elinucknack/door-sensor/door-sensor-pcb.kicad_sch

## KiCad design door-sensor-pcb.kicad_sch (2025-08-03)

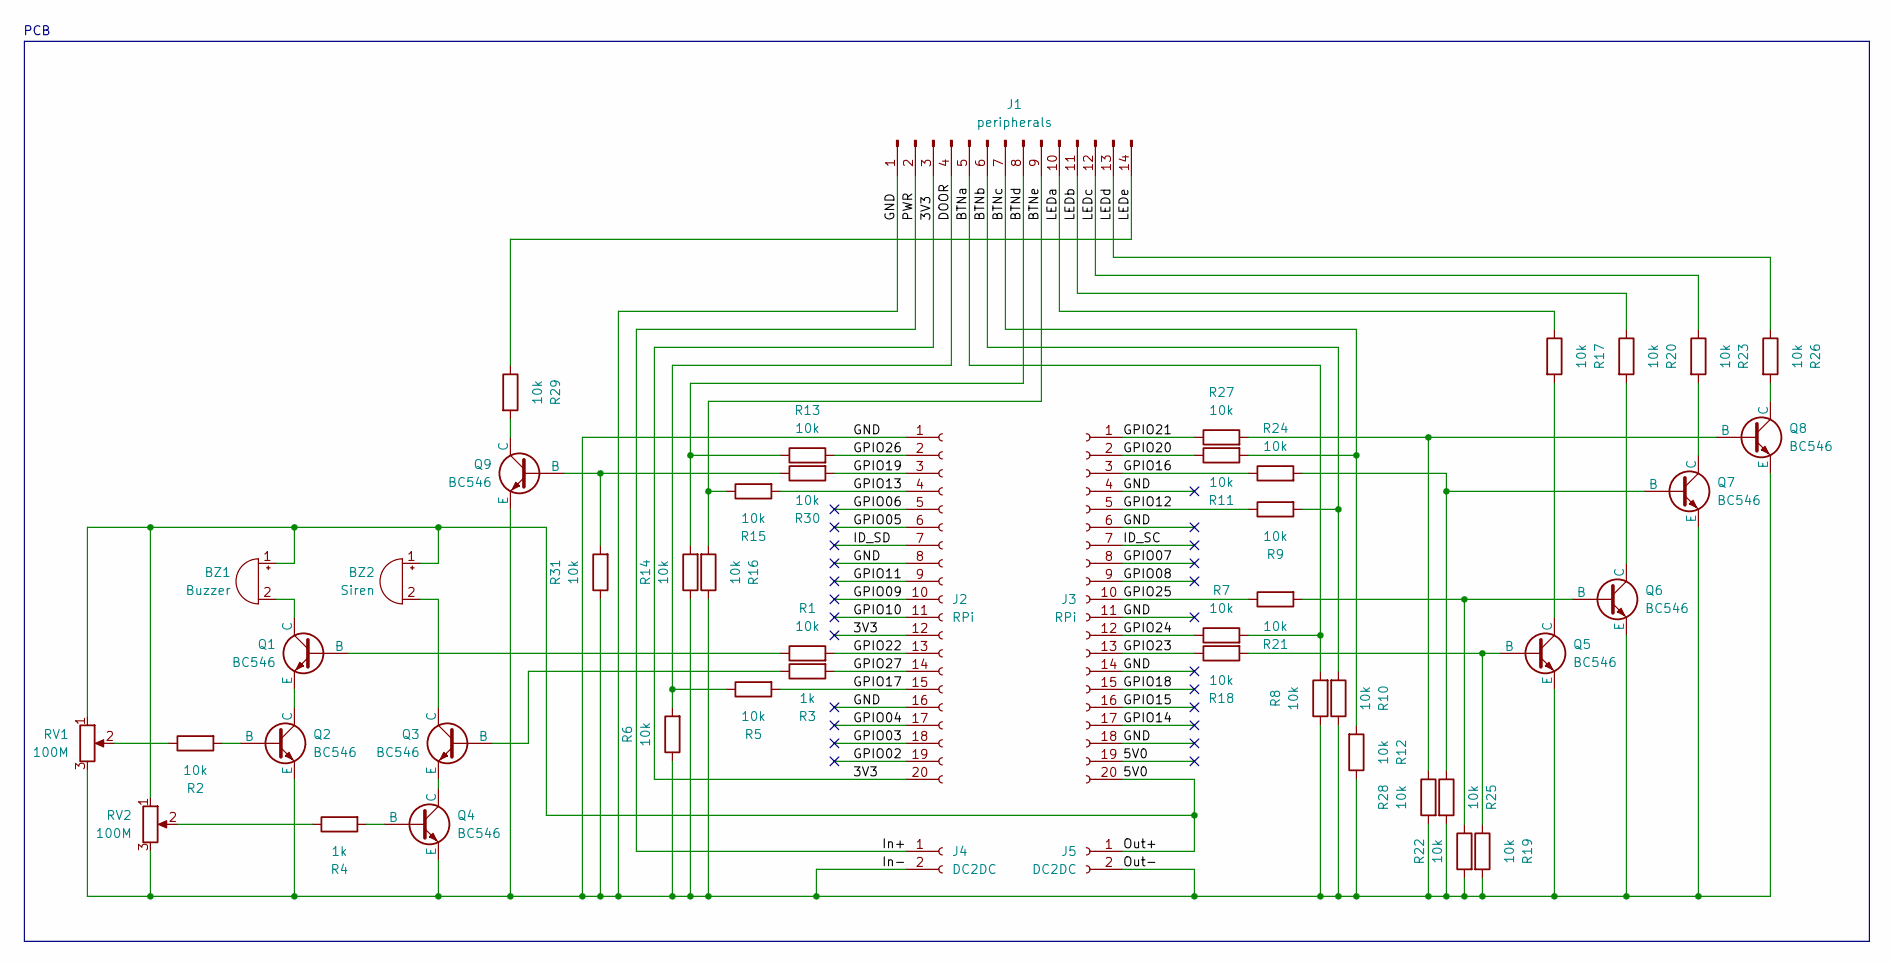
[picture p12: schematic door-sensor-pcb.kicad_sch]

Parts:
BZ1: Buzzer
BZ2: Siren
J1: peripherals
J2, J3: RPi
J4, J5: DC2DC
Q1, Q2, Q3, Q4, Q5, Q6, Q7, Q8, Q9: BC546
R1, R2, R5, R6, R7, R8, R9, R10, R11, R12, R13, R14, R15, R16, R17, R18, R19, R20, R21, R22, R23, R24, R25, R26, R27, R28, R29, R30, R31: 10k
R3, R4: 1k
RV1, RV2: 100M

Connections:
3V3: J1.3, J2.12, J2.20
5V0: BZ1.1 (+), BZ2.1 (+), J3.19, J3.20, J5.1, RV1.1, RV2.1
BTNa: J1.5, R7.2, R8.2
BTNb: J1.6, R9.2, R10.2
BTNc: J1.7, R11.2, R12.2
BTNd: J1.8, R13.1, R14.2
BTNe: J1.9, R15.1, R16.2
DOOR: J1.4, R5.1, R6.2
GND: J1.1, J2.1, J2.8, J2.16, J3.4, J3.6, J3.11, J3.14, J3.18, J4.2, J5.2, Q2.3 (E), Q4.3 (E), Q5.3 (E), Q6.3 (E), Q7.3 (E), Q8.3 (E), Q9.3 (E), R6.1, R8.1, R10.1, R12.1, R14.1, R16.1, R19.2, R22.2, R25.2, R28.2, R31.1, RV1.3, RV2.3
GPIO02: J2.19
GPIO03: J2.18
GPIO04: J2.17
GPIO05: J2.6
GPIO06: J2.5
GPIO07: J3.8
GPIO08: J3.9
GPIO09: J2.10
GPIO10: J2.11
GPIO11: J2.9
GPIO12: J3.5, R9.1
GPIO13: J2.4, R15.2
GPIO14: J3.17
GPIO15: J3.16
GPIO16: J3.3, R24.1
GPIO17: J2.15, R5.2
GPIO18: J3.15
GPIO19: J2.3, R30.2
GPIO20: J3.2, R11.1
GPIO21: J3.1, R27.1
GPIO22: J2.13, R1.2
GPIO23: J3.13, R18.1
GPIO24: J3.12, R7.1
GPIO25: J3.10, R21.1
GPIO26: J2.2, R13.2
GPIO27: J2.14, R3.2
ID_SC: J3.7
ID_SD: J2.7
In+: J1.2, J4.1
LEDa: J1.10, R17.1
LEDb: J1.11, R20.1
LEDc: J1.12, R23.1
LEDd: J1.13, R26.1
LEDe: J1.14, R29.1
unnamed: BZ1.2 (-), Q1.1 (C)
unnamed: BZ2.2 (-), Q3.1 (C)
unnamed: Q1.2 (B), R1.1
unnamed: Q1.3 (E), Q2.1 (C)
unnamed: Q2.2 (B), R2.2
unnamed: Q3.2 (B), R3.1
unnamed: Q3.3 (E), Q4.1 (C)
unnamed: Q4.2 (B), R4.2
unnamed: Q5.1 (C), R17.2
unnamed: Q5.2 (B), R18.2, R19.1
unnamed: Q6.1 (C), R20.2
unnamed: Q6.2 (B), R21.2, R22.1
unnamed: Q7.1 (C), R23.2
unnamed: Q7.2 (B), R24.2, R25.1
unnamed: Q8.1 (C), R26.2
unnamed: Q8.2 (B), R27.2, R28.1
unnamed: Q9.1 (C), R29.2
unnamed: Q9.2 (B), R30.1, R31.2
unnamed: R2.1, RV1.2
unnamed: R4.1, RV2.2

Notes on the sheet:
PCB
