elinucknack/door-sensor/door-sensor-peripherals.kicad_sch

## KiCad design door-sensor-peripherals.kicad_sch (2025-07-26)

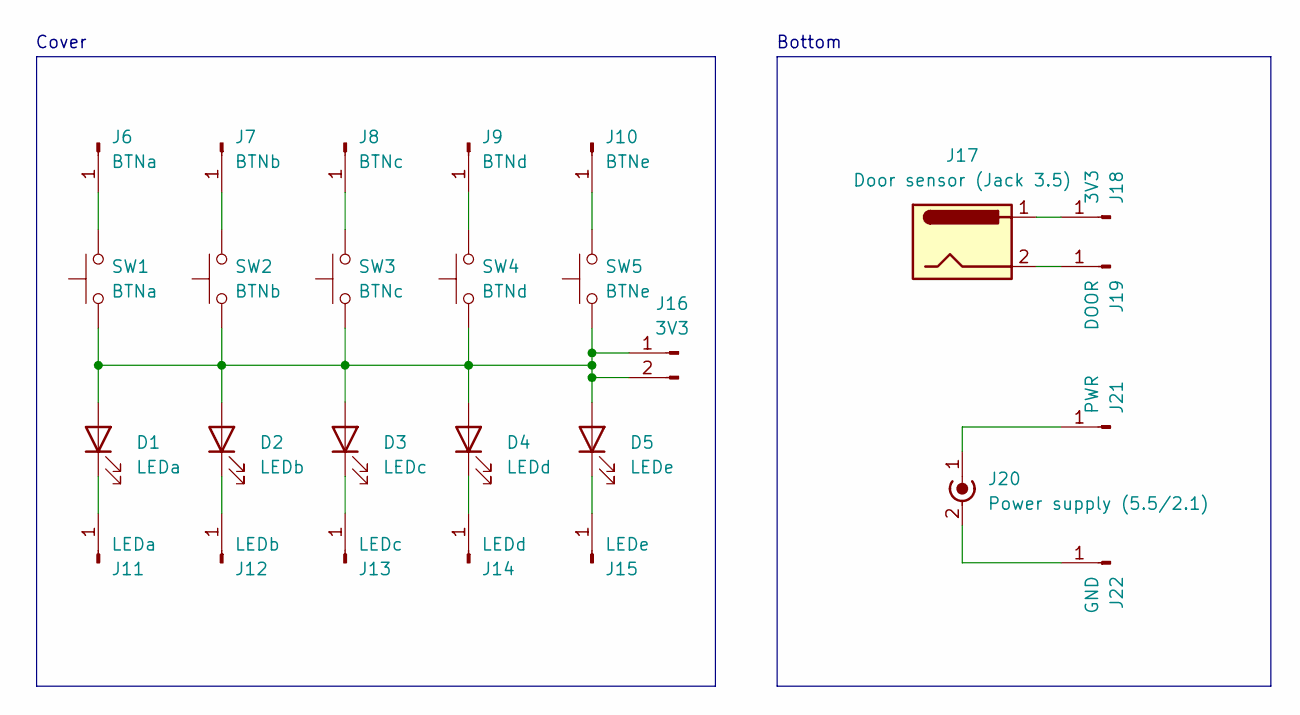
[picture p13: schematic door-sensor-peripherals.kicad_sch]

Parts:
D1: LEDa
D2: LEDb
D3: LEDc
D4: LEDd
D5: LEDe
J6: BTNa
J7: BTNb
J8: BTNc
J9: BTNd
J10: BTNe
J11: LEDa
J12: LEDb
J13: LEDc
J14: LEDd
J15: LEDe
J16, J18: 3V3
J17: Door sensor (Jack 3.5)
J19: DOOR
J20: Power supply (5.5/2.1)
J21: PWR
J22: GND
SW1: BTNa
SW2: BTNb
SW3: BTNc
SW4: BTNd
SW5: BTNe

Connections:
unnamed: D1.1 (K), J11.1
unnamed: D1.2 (A), D2.2 (A), D3.2 (A), D4.2 (A), D5.2 (A), J16.1, J16.2, SW1.1, SW2.1, SW3.1, SW4.1, SW5.1
unnamed: D2.1 (K), J12.1
unnamed: D3.1 (K), J13.1
unnamed: D4.1 (K), J14.1
unnamed: D5.1 (K), J15.1
unnamed: J6.1, SW1.2
unnamed: J7.1, SW2.2
unnamed: J8.1, SW3.2
unnamed: J9.1, SW4.2
unnamed: J10.1, SW5.2
unnamed: J17.1, J18.1
unnamed: J17.2, J19.1
unnamed: J20.1 (In), J21.1
unnamed: J20.2 (Ext), J22.1

Notes on the sheet:
Cover
Bottom
